mru00/SampleScope/kicad/Analog.sch

## KiCad design kicad/Analog.sch (2012-05-17)

Schematic: Analog.sch

Parts:
C1, C2: C
C8, C9: 100n
C10: 4u7
D1, D2, D3, D4, D5, D6, D7, D8: DIODE
P1: Test.Ch1.PostGain
P2: Test.Ch2.PostGain
P3: Test.Ch1.PostOffset
P4: Test.Ch2.PostOffset
P5: Test.Ch1.PostACDC
P6: Test.Ch2.PostACDC
R1, R2: 33k
R3, R4, R11, R12: 100k
R5, R6, R7, R8: 10k
R9, R10: 95k
RV1, RV2, RV3, RV4: 10k
U1: MAX532
U5: MAX114
U8: MAX4622
U16, U17: TLE2084
W1, W2: TEST

Notes on the sheet:
Level clamping
ADC
level shifter -12..+12V -> 0..5V
programmable gain amplifier
AC / DC decoupler
Input Buffer
