mru00/SampleScope/kicad/MCU.sch

## KiCad design kicad/MCU.sch (2012-05-17)

Schematic: MCU.sch

Parts:
C3, C4: 22p
C5: u220
C6, C7: 100n
D9: LED
J1: USB_2
P10: ICSP
R16: 10k
R17: 120R
U6: PIC18F4450
X1: 20MHz
