mru00/SampleScope/kicad/supply.sch

## KiCad design kicad/supply.sch (2012-05-17)

Schematic: supply.sch

Parts:
P7: IQ0515S
P8: Virt_GND_Conn
P9: Test.Vref.2.5
P11: Test.Vref.4.094
P12: Test.Vref.5.0
U3: MAX6241
U9: MAX6225
U13: MAX6250

Notes on the sheet:
voltage references
pseudo element represents single point of connection between AGND and DGND
DC DC converter
