mru00/SampleScope/kicad/trigger.sch

## KiCad design kicad/trigger.sch (2012-05-17)

Schematic: trigger.sch

Parts:
P13: MAX942
U2: MAX532

Notes on the sheet:
Comparator
Threshold voltage
