mru00/SampleScope/pcb/gen.sch

## KiCad design pcb/gen.sch (2012-05-01)

Schematic: gen.sch

Parts:
C5: 10u
C6, C9: C
C7: u1
C8: u01
P9: DIL8
P11: AD9833
