mru00/SampleScope/firmware/Firmware/config_bits.h

/** CONFIGURATION **************************************************/

#pragma config PLLDIV   = 5         // (20 MHz crystal on PICDEM FS USB board)
#pragma config CPUDIV   = OSC1_PLL2
#pragma config USBDIV   = 2         // Clock source from 96MHz PLL/2
#pragma config FOSC     = HSPLL_HS
#pragma config FCMEN    = OFF
#pragma config IESO     = OFF
#pragma config PWRT     = ON
#pragma config BOR      = OFF
//#pragma config BORV     = 28
#pragma config VREGEN   = ON      //USB Voltage Regulator
#pragma config WDT      = OFF
#pragma config WDTPS    = 32768
#pragma config MCLRE    = ON
#pragma config LPT1OSC  = OFF
#pragma config PBADEN   = OFF
//      #pragma config CCP2MX   = ON
#pragma config STVREN   = ON
#pragma config LVP      = OFF
//      #pragma config ICPRT    = OFF       // Dedicated In-Circuit Debug/Programming
#pragma config XINST    = OFF       // Extended Instruction Set
#pragma config CP0      = OFF
#pragma config CP1      = OFF
//      #pragma config CP2      = OFF
//      #pragma config CP3      = OFF
#pragma config CPB      = OFF
//      #pragma config CPD      = OFF
#pragma config WRT0     = OFF
#pragma config WRT1     = OFF
//      #pragma config WRT2     = OFF
//      #pragma config WRT3     = OFF
#pragma config WRTB     = OFF       // Boot Block Write Protection
#pragma config WRTC     = OFF
//      #pragma config WRTD     = OFF
#pragma config EBTR0    = OFF
#pragma config EBTR1    = OFF
//      #pragma config EBTR2    = OFF
//      #pragma config EBTR3    = OFF
#pragma config EBTRB    = OFF
