mru00/SampleScope/frontend/Osci/lmmin.h

/*
 * Project LevenbergMarquardtLeastSquaresFitting
 *        (more info in lmmin.c)
 *
 * File lmmin.h (C) Joachim Wuttke 2004-8 www.messen-und-deuten.de/lmfit
 *
 * Public interface to the Levenberg-Marquardt core implementation.
 */
 
#ifndef LMMIN_H
#define LMMIN_H

#ifdef __cplusplus
extern "C" {
#endif


//** User-supplied subroutines. **/

/* Type of user-supplied subroutine that calculates fvec. */
typedef void (lm_evaluate_ftype) (double *par, int m_dat, double *fvec,
				  void *data, int *info);

/* Default implementation therof, provided by lm_eval.c. */
void lm_evaluate_default(double *par, int m_dat, double *fvec, void *data,
			 int *info);

/* Type of user-supplied subroutine that informs about fit progress. */
typedef void (lm_print_ftype) (int n_par, double *par, int m_dat,
			       double *fvec, void *data, int iflag,
			       int iter, int nfev);

/* Default implementation therof, provided by lm_eval.c. */
void lm_print_default(int n_par, double *par, int m_dat, double *fvec,
		      void *data, int iflag, int iter, int nfev);


/** Compact high-level interface. **/

/* Collection of control parameters. */
typedef struct {
    double ftol;      /* relative error desired in the sum of squares. */
    double xtol;      /* relative error between last two approximations. */
    double gtol;      /* orthogonality desired between fvec and its derivs. */
    double epsilon;   /* step used to calculate the jacobian. */
    double stepbound; /* initial bound to steps in the outer loop. */
    double fnorm;     /* norm of the residue vector fvec. */
    int maxcall;      /* maximum number of iterations. */
    int nfev;	      /* actual number of iterations. */
    int info;	      /* status of minimization. */
} lm_control_type;

/* Initialize control parameters with default values. */
void lm_initialize_control(lm_control_type * control);

/* Refined calculation of Eucledian norm, typically used in printout routine. */
double lm_enorm(int, double *);

/* The actual minimization. */
void lm_minimize(int m_dat, int n_par, double *par,
		 lm_evaluate_ftype * evaluate, lm_print_ftype * printout,
		 void *data, lm_control_type * control);

/** Legacy low-level interface. **/

/* Alternative to lm_minimize, allowing full control, and read-out
   of auxiliary arrays. For usage, see implementation of lm_minimize. */
void lm_lmdif(int m, int n, double *x, double *fvec, double ftol,
	      double xtol, double gtol, int maxfev, double epsfcn,
	      double *diag, int mode, double factor, int *info, int *nfev,
	      double *fjac, int *ipvt, double *qtf, double *wa1,
	      double *wa2, double *wa3, double *wa4,
	      lm_evaluate_ftype * evaluate, lm_print_ftype * printout,
	      void *data);


#ifndef _LMDIF
extern const char *lm_infmsg[];
extern const char *lm_shortmsg[];
#endif

#ifdef __cplusplus
}
#endif

#endif /* LMMIN_H */
